mariusares/RoboFarm/CeresOne/Resources/psu.jpg

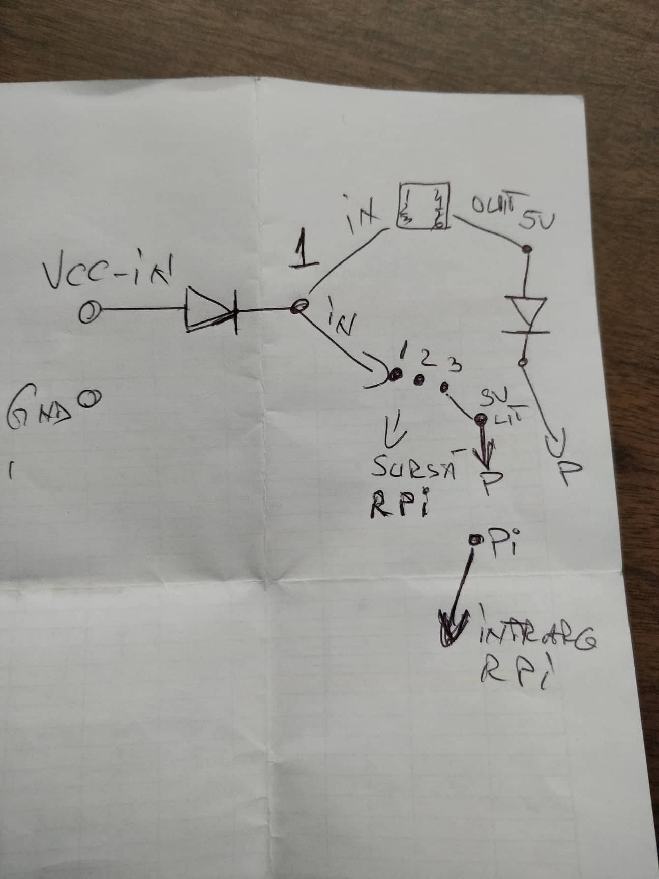
CeresOne/Resources/psu.jpg
