mariusares/RoboFarm/CeresOne/Previews/Bottom Preview.png

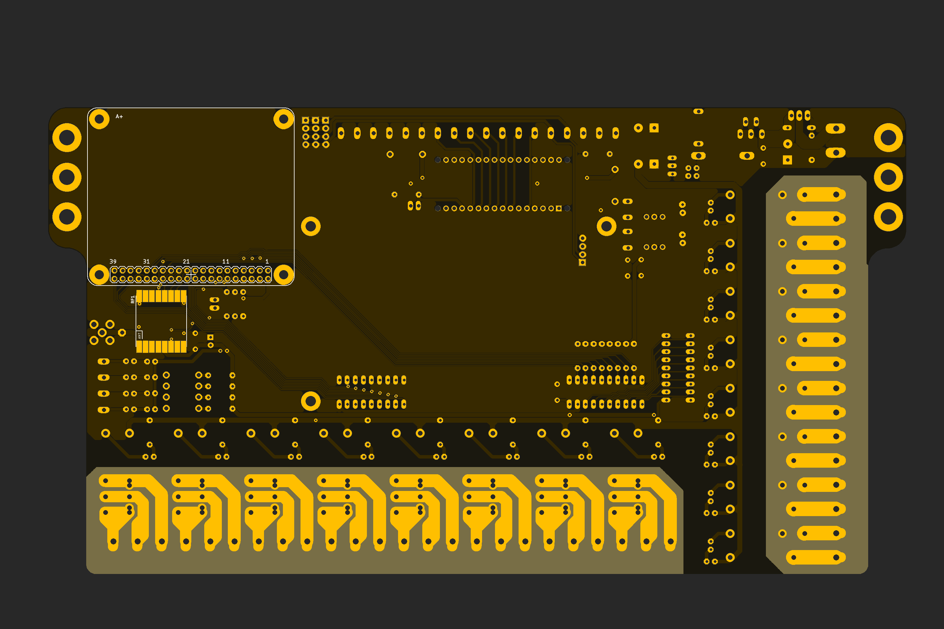
CeresOne/Previews/Bottom Preview.png
