mariusares/RoboFarm/CeresOne/Previews/Top Preview.png

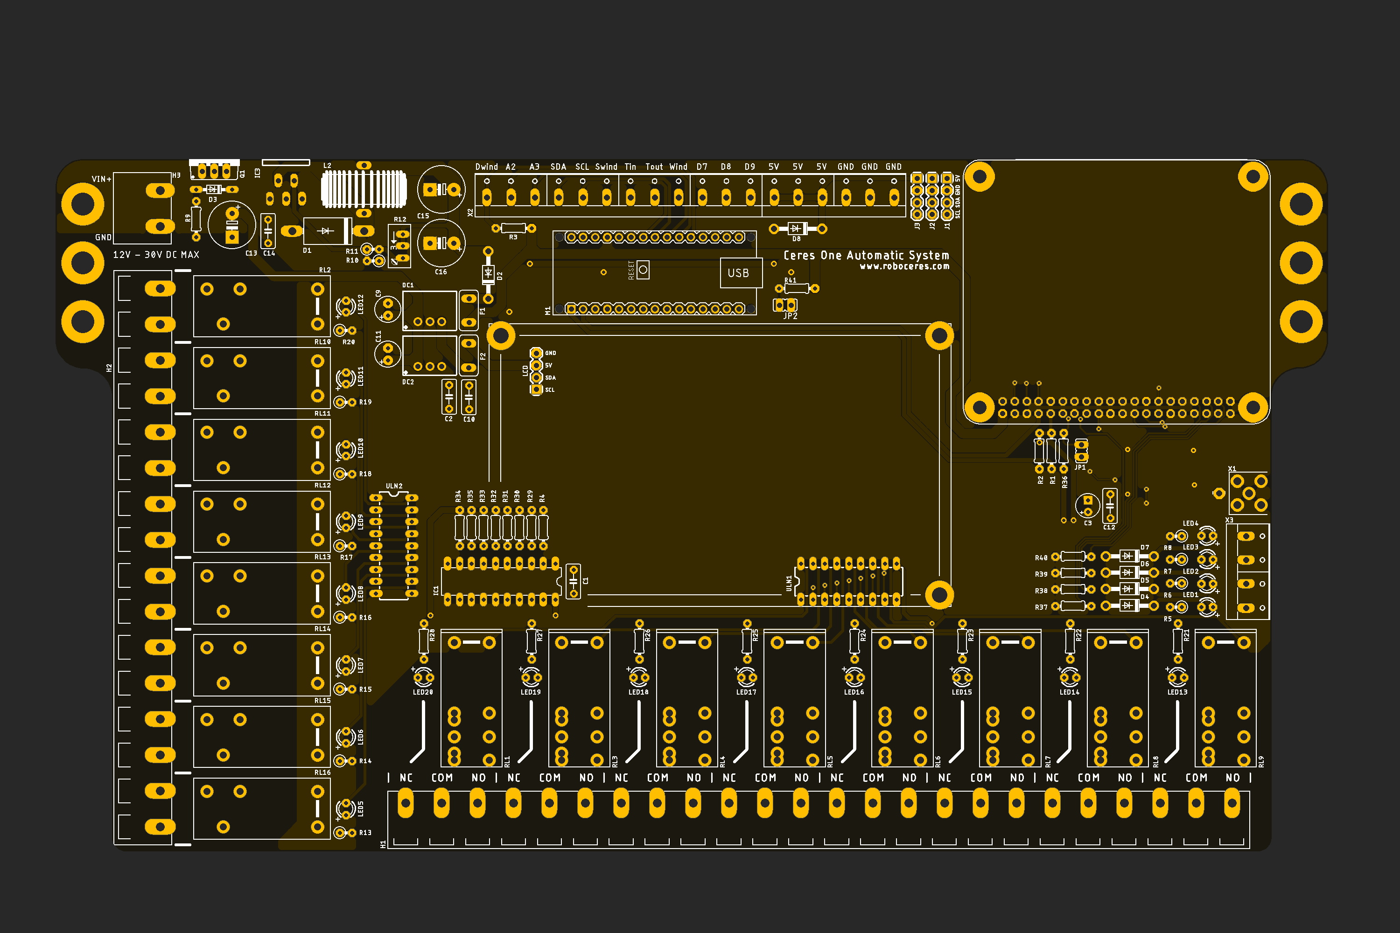
CeresOne/Previews/Top Preview.png
