mariusares/RoboFarm/CeresOne/Resources/radio module 1.jpg

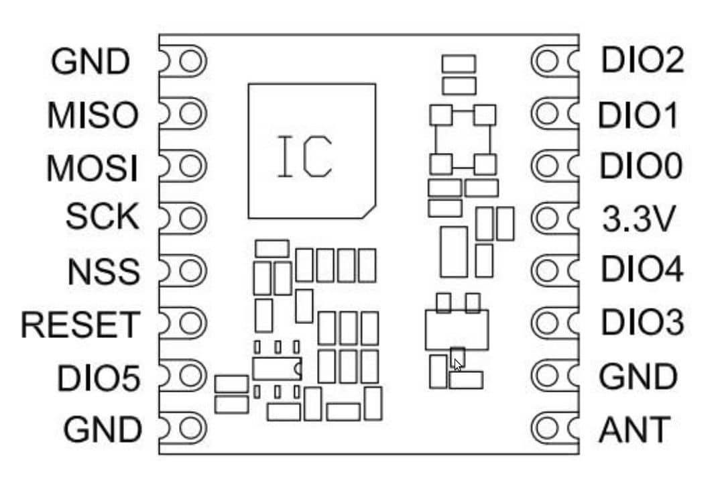
CeresOne/Resources/radio module 1.jpg
