mariusares/RoboFarm/CeresOne/Resources/radio module 2.jpg

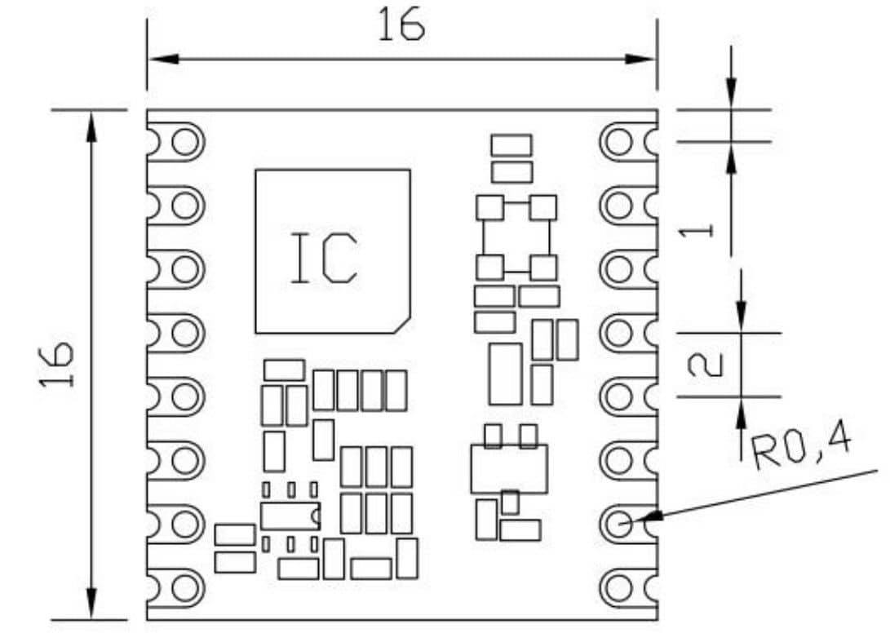
CeresOne/Resources/radio module 2.jpg
