mariusares/RoboFarm/html/img/1wq.png

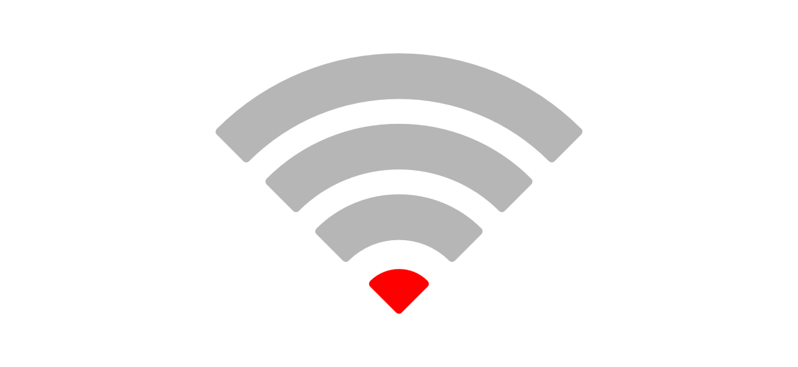
html/img/1wq.png
