mariusares/RoboFarm/png/gui2.png

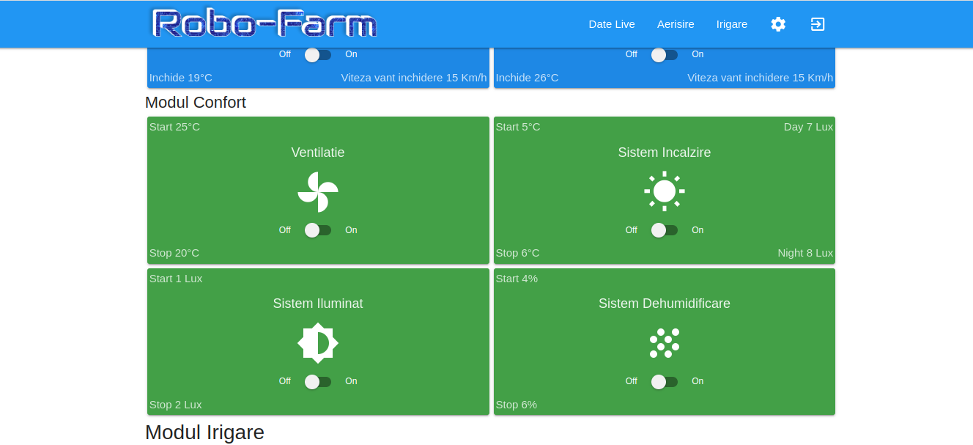
png/gui2.png
