mariusares/RoboFarm/png/gui3.png

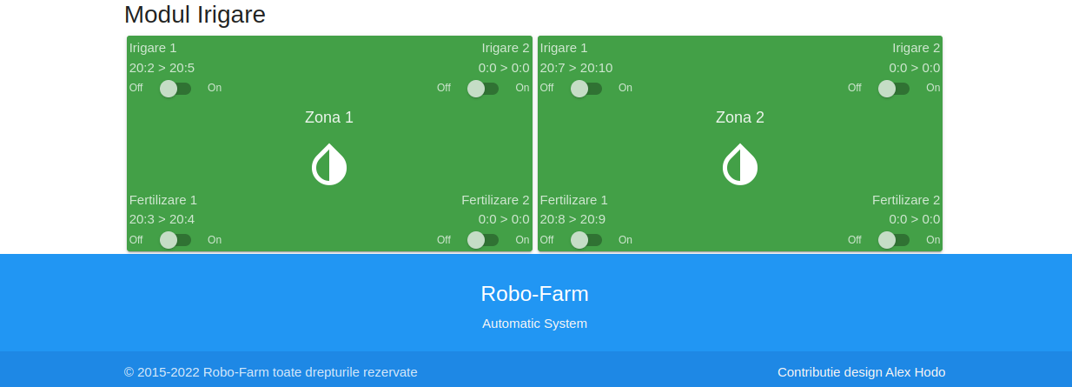
png/gui3.png
