mariusares/RoboFarm/png/gui.png

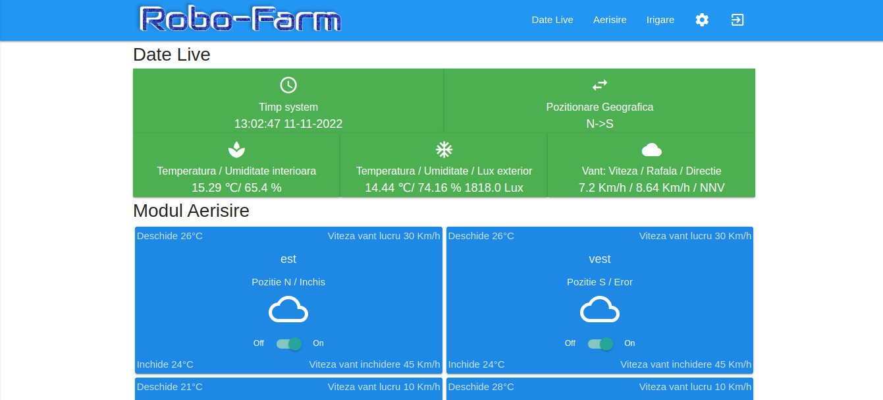
png/gui.png
