mariusares/RoboFarm/png/network.png

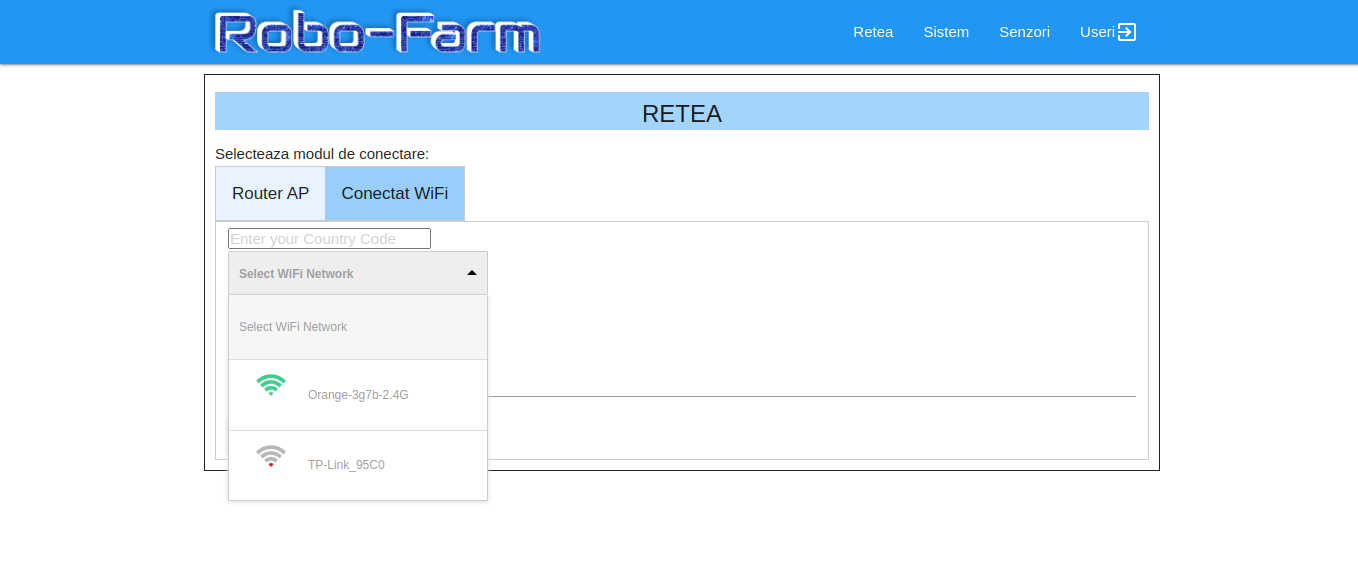
png/network.png
