mariusares/RoboFarm/png/system.png

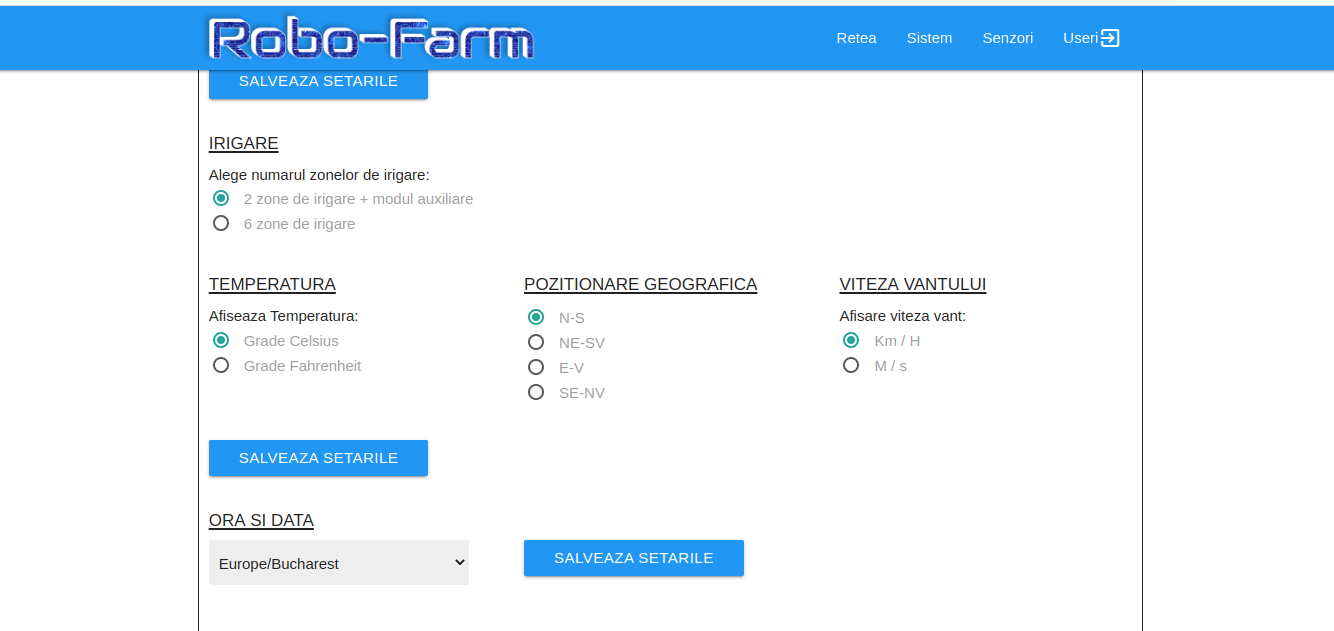
png/system.png
